JJOmin/Projektgruppe-Smarter-Blumentopf/3dModel/STL_Dateien/TopfDreigeteiltMitte.stl

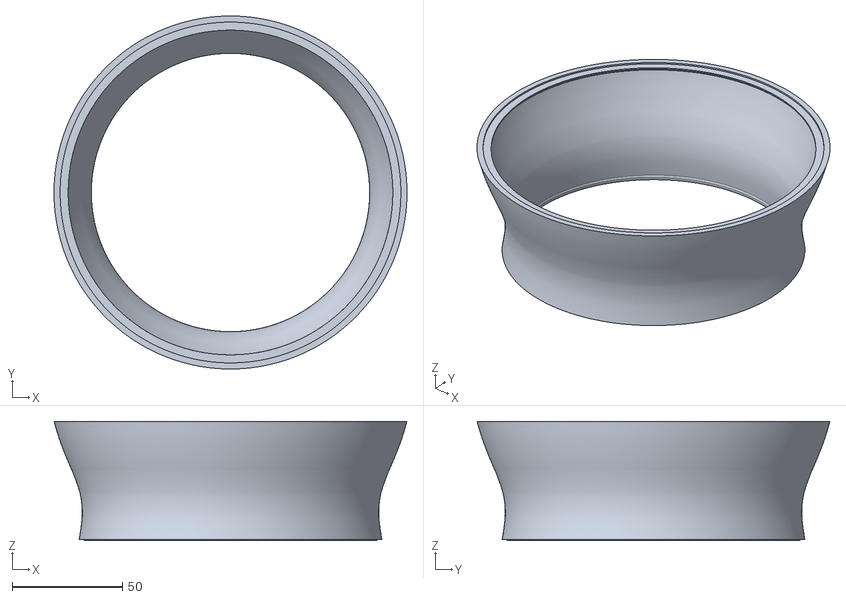
[picture p57: CAD file, 2024-02-22]
3dModel/STL_Dateien/TopfDreigeteiltMitte.stl
160.4 x 160.4 x 54.1
