JJOmin/Projektgruppe-Smarter-Blumentopf/Archiv/3dModelArchiv/andere größe/Boden.stl

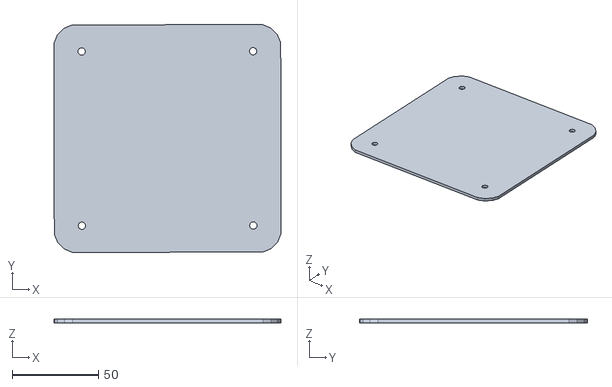
[picture p58: CAD file, 2023-12-12, an earlier design]
Archiv/3dModelArchiv/andere größe/Boden.stl
131.6 x 132.0 x 2.03
