JJOmin/Projektgruppe-Smarter-Blumentopf/Archiv/3dModelArchiv/Schraubenunten.stl

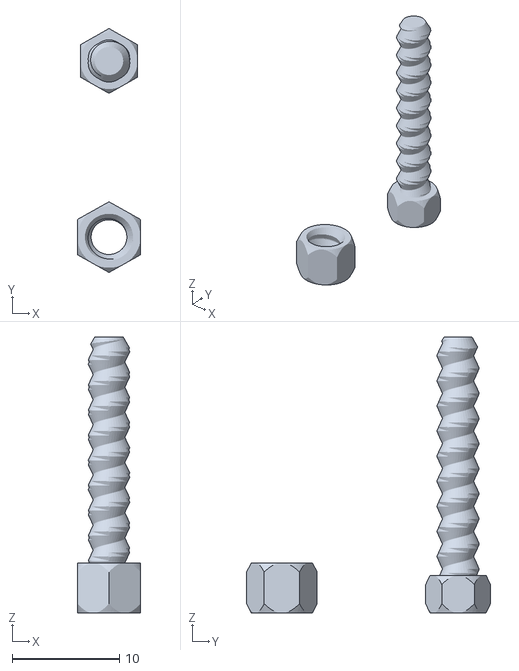
[picture p59: CAD file, 2023-12-13, an earlier design]
Archiv/3dModelArchiv/Schraubenunten.stl
5.88 x 22.8 x 25.8
