JJOmin/Projektgruppe-Smarter-Blumentopf/Finale Abgabe/src offline/TemperatureSensor.py

import machine, onewire, ds18x20, time

class TemperatureSensor:
    def __init__(self, tempData): #btn_pin
        self.ds_pin = machine.Pin(tempData['dpin']) # pin für Sensor
        self.ds_sensor = ds18x20.DS18X20(onewire.OneWire(self.ds_pin)) # Kominikation mit Sensor
        self.roms = self.ds_sensor.scan() #Suche nach DS18B20-Sensoren
        self.running = False # Maybe muss das true sein(noch nicht sicher)
        #print('Found DS devices: ', self.roms) #Ausgabe der gefundenen Adressen:
        #self.btnColor = machine.Pin(btn_pin, machine.Pin.IN) # Taster

    def readTemperature(self): #Funktion ließ die Temperatur 
        self.ds_sensor.convert_temp() #Umwandlung (koventierung) der werte in Temperatur werte
        time.sleep_ms(750) #pause würde ich empfehlen 
        for rom in self.roms: # solange self.roms werte ließt
            temperature = self.ds_sensor.read_temp(rom) # temperatur = die gelesenen Koventierten werte
            #print("Temperatur: {:.2f}°C".format(temperature)) #Ausgabe der Temperatur + Formatierung
            return temperature

#     def start_by_press(self): # die schleife wird ausgeführt wenn der taster gedrückt wird
#         self.running = True # Start variable die abgefragt wird um start_by_press zu beenden.
#         while self.running: # endloschschleife solange 
#             self.read_temperature() # Starte die methode read_temperatur() Also ließ
             #if self.btnColor.value() == 0: #Wenn sich der Wert vom knopf ändert
#                 self.running = False # Setze die Prüf variable auf false damit die funktion start_by_press nicht mehr ausgeführt wird
#                 break
            

# Instanzierung der Klasse. Instanzierung in die Main??? 
#temperatur_sensor = Temperatur(ds_pin=22, btn_pin=34) #wichtig geht nur mit Pin22

#while True: # Endlosschleife die darauf wartet das Btn gedrückt wird und dann Methoden istanziert
    #if temperatur_sensor.btnColor.value(): # wenn der wert vom btn True ist
     #   temperatur_sensor.read_temperature() # Startet diese Methode
